mikaelmarvin/gambos-sw/software/project/app/devkit/app/app.hpp

/**
 * @file app.hpp
 * @brief Application layer – devkit (test code).
 */

#ifndef GAMBOS_APP_HPP
#define GAMBOS_APP_HPP

#ifdef __cplusplus
extern "C" {
#endif

void app_init(void);
void app_run(void);

#ifdef __cplusplus
}
#endif

#endif /* GAMBOS_APP_HPP */
