mikaelmarvin/gambos-sw/software/project/board/devkit/Core/Src/gpio.c

#include "gpio.h"

/** Configure pins as
 * Analog
 * Input
 * Output
 * EVENT_OUT
 * EXTI
 */
void MX_GPIO_Init(void) {

    GPIO_InitTypeDef GPIO_InitStruct = {0};

    /* GPIO Ports Clock Enable */
    __HAL_RCC_GPIOC_CLK_ENABLE();
    __HAL_RCC_GPIOH_CLK_ENABLE();
    __HAL_RCC_GPIOA_CLK_ENABLE();
    __HAL_RCC_GPIOB_CLK_ENABLE();

    /*Configure GPIO pin Output Level */
    HAL_GPIO_WritePin(LD2_GPIO_Port, LD2_Pin, GPIO_PIN_RESET);

    /*Configure GPIO pin Output Level */
    HAL_GPIO_WritePin(GPIOC, CS2_Pin | CS1_Pin, GPIO_PIN_RESET);

    /*Configure GPIO pin : B1_Pin */
    GPIO_InitStruct.Pin = B1_Pin;
    GPIO_InitStruct.Mode = GPIO_MODE_IT_RISING_FALLING;
    GPIO_InitStruct.Pull = GPIO_NOPULL;
    HAL_GPIO_Init(B1_GPIO_Port, &GPIO_InitStruct);

    /*Configure GPIO pin : LD2_Pin */
    GPIO_InitStruct.Pin = LD2_Pin;
    GPIO_InitStruct.Mode = GPIO_MODE_OUTPUT_PP;
    GPIO_InitStruct.Pull = GPIO_NOPULL;
    GPIO_InitStruct.Speed = GPIO_SPEED_FREQ_LOW;
    HAL_GPIO_Init(LD2_GPIO_Port, &GPIO_InitStruct);

    /*Configure GPIO pins : CS2_Pin CS1_Pin */
    GPIO_InitStruct.Pin = CS2_Pin | CS1_Pin;
    GPIO_InitStruct.Mode = GPIO_MODE_OUTPUT_PP;
    GPIO_InitStruct.Pull = GPIO_NOPULL;
    GPIO_InitStruct.Speed = GPIO_SPEED_FREQ_LOW;
    HAL_GPIO_Init(GPIOC, &GPIO_InitStruct);

    /* EXTI interrupt init*/
    HAL_NVIC_SetPriority(EXTI15_10_IRQn, 5, 0);
    HAL_NVIC_EnableIRQ(EXTI15_10_IRQn);
}
