mikaelmarvin/gambos-sw/software/project/app/devkit/button_handler/common.hpp

#ifndef GAMBOS_BUTTON_HANDLER_COMMON_HPP
#define GAMBOS_BUTTON_HANDLER_COMMON_HPP

#include <stdint.h>

enum class ButtonId : uint8_t {
    USER_BUTTON = 0U,
};

#endif /* GAMBOS_BUTTON_HANDLER_COMMON_HPP */
